chemistorge/Arduino-Motorised-Filter-Wheel-Xagyl-compatible-ASCOM-and-INDI-/Filter Wheel Side.jpg

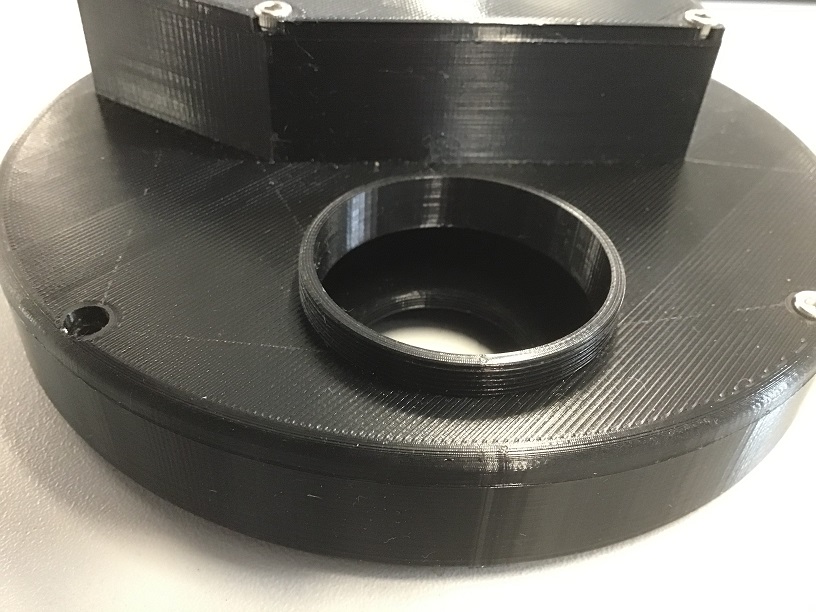
Filter Wheel Side.jpg
