chemistorge/Arduino-Motorised-Filter-Wheel-Xagyl-compatible-ASCOM-and-INDI-/Filter Wheel with Camera 2.jpeg

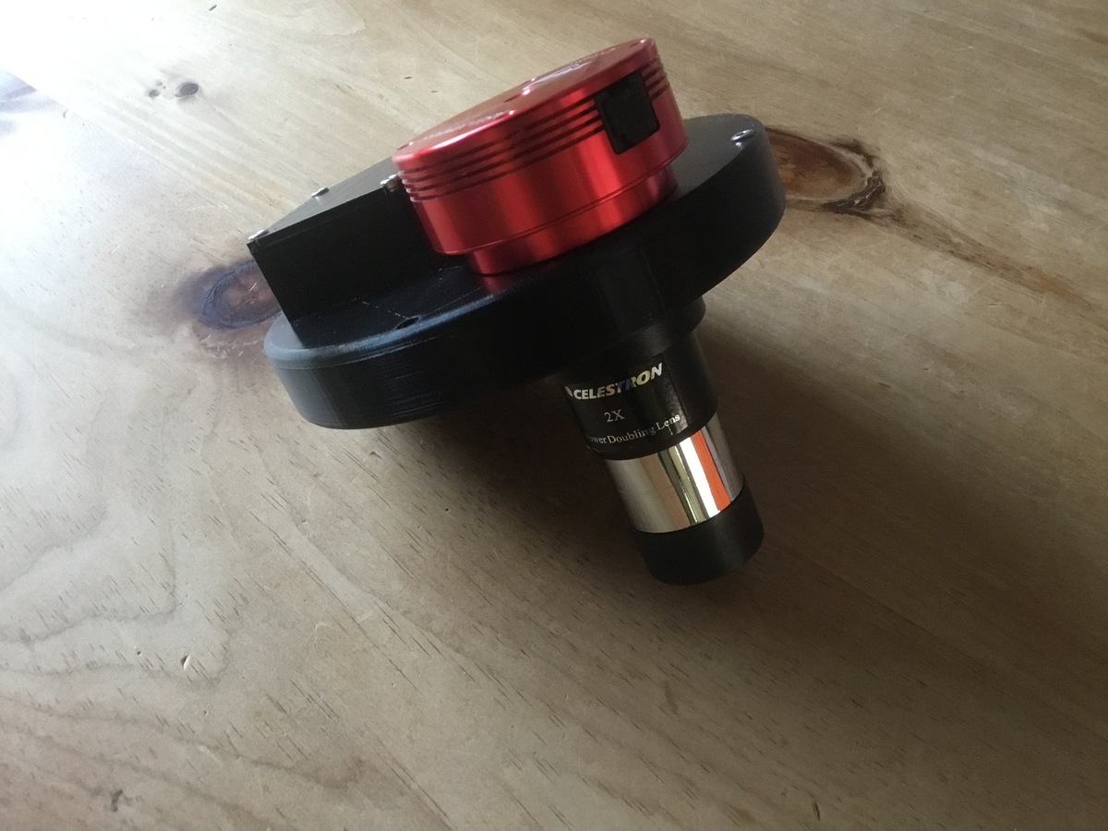
Filter Wheel with Camera 2.jpeg
